MartinDavidWaller/SEMI-AUTOMATIC-BUG-key---From-the-ground-up/Pictures/Keyer 1.jpg

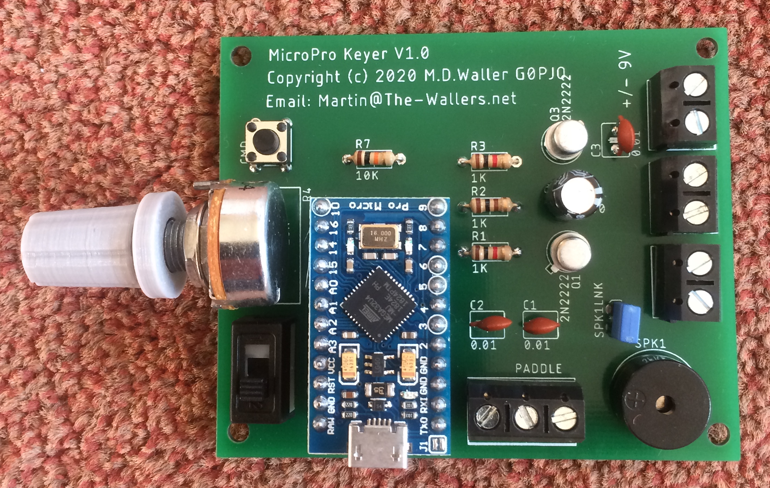
Pictures/Keyer 1.jpg
