MartinDavidWaller/SEMI-AUTOMATIC-BUG-key---From-the-ground-up/Pictures/Keyer 2.jpg

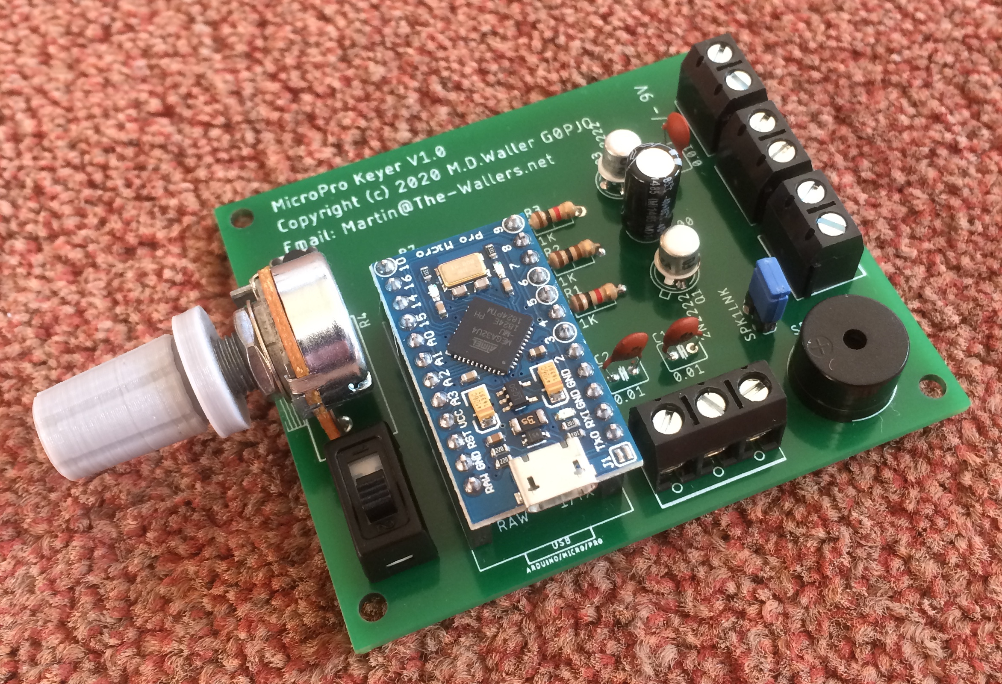
Pictures/Keyer 2.jpg
